AlperenAkkuncu/PlainDAQ/pics/plaindaq-band-pass.png

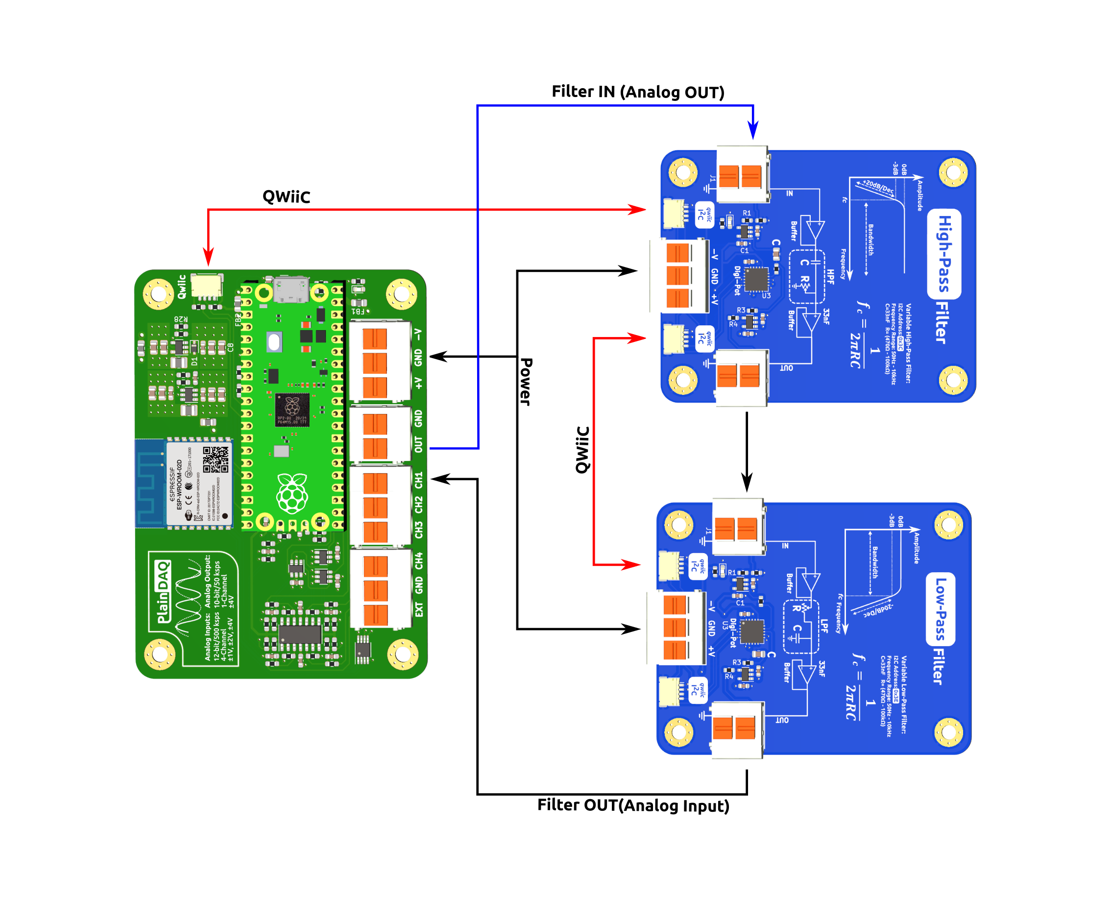
pics/plaindaq-band-pass.png
