AlperenAkkuncu/PlainDAQ/pics/plaindaq-high-pass.png

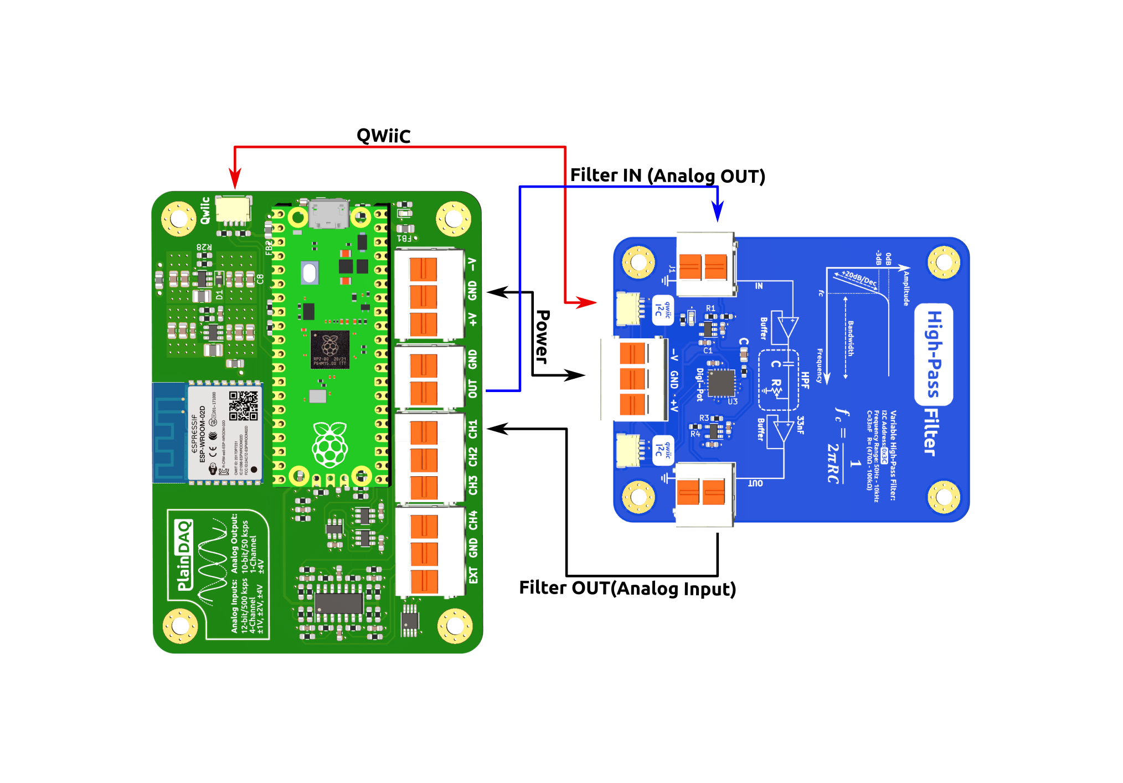
pics/plaindaq-high-pass.png
