AlperenAkkuncu/PlainDAQ/Development/SPICE_simulation/DAC_reconstruction/DAC_reconstruction.asc

C1: cap; 4.3n
C2: cap; 1.1n
C3: cap; 4.3n
C4: cap; 1.1n
C5: cap; 4.3n
C6: cap; 1.1n
R1: res; 2.05k
R2: res; 1.02k
R3: res; 2.05k
R4: res; 2.05k
R5: res; 2.05k
R6: res; 2.05k
R7: res; 2.05k
R8: res; 2.05k
R9: res; 2.05k
R10: res; 2.05k
R11: res; 2.05k
R12: res; 1.02k
R13: res; 2.05k
R14: res; 2.05k
R15: res; 2.05k
R16: res; 2.05k
R17: res; 2.05k
R18: res; 2.05k
R19: res; 2.05k
R20: res; 2.05k
R21: res; 2.05k
R22: res; 2.05k
R23: res; 1.02k
R24: res; 2.05k
R25: res; 2.05k
R26: res; 2.05k
R27: res; 2.05k
R28: res; 2.05k
R29: res; 2.05k
R30: res; 2.05k
R31: res; 2.05k
R32: res; 2.05k
R33: res; 2.05k
R34: res; 2.05k
R35: res; 2.05k
R36: res; 2.05k
R37: res; 2.05k
R38: res; 2.05k
U1: opamp2; TL072
U2: opamp2; TL072
U3: opamp2; TL072
U4: opamp2; TL072
U5: opamp2; TL072
U6: opamp2; TL072
U7: opamp2; TL072
U8: opamp2; TL072
U9: opamp2; TL072
U10: opamp2; TL072
U11: opamp2; TL072
V1: voltage; 6.5
V2: voltage; 6.5
V3: voltage; SINE(1 1 1k); AC 1
V4: voltage; 4
V5: voltage; SINE(1 1 1k); AC 1
V6: voltage; 4
V7: voltage; 1; AC 0
V8: voltage; SINE(1 1 1k); AC 1
V9: voltage; 0.8; AC 0
V10: voltage; 1; AC 0
V11: voltage; 4.096; AC 0
V12: voltage; 4.096; AC 0
Named nets: 0, +V, -V
* TL072 OPERATIONAL AMPLIFIER "MACROMODEL" SUBCIRCUIT
* CREATED USING PARTS RELEASE 4.01 ON 06/16/89 AT 13:08
* (REV N/A)      SUPPLY VOLTAGE: +/-15V
* CONNECTIONS:   NON-INVERTING INPUT
*                | INVERTING INPUT
*                | | POSITIVE POWER SUPPLY
*                | | | NEGATIVE POWER SUPPLY
*                | | | | OUTPUT
*                | | | | |
.SUBCKT TL072    1 2 3 4 5
*
  C1   11 12 3.498E-12
  C2    6  7 15.00E-12
  DC    5 53 DX
  DE   54  5 DX
  DLP  90 91 DX
  DLN  92 90 DX
  DP    4  3 DX
  EGND 99  0 POLY(2) (3,0) (4,0) 0 .5 .5
  FB    7 99 POLY(5) VB VC VE VLP VLN 0 4.715E6 -5E6 5E6 5E6 -5E6
  GA    6  0 11 12 282.8E-6
  GCM   0  6 10 99 8.942E-9
  ISS   3 10 DC 195.0E-6
  HLIM 90  0 VLIM 1K
  J1   11  2 10 JX
  J2   12  1 10 JX
  R2    6  9 100.0E3
  RD1   4 11 3.536E3
  RD2   4 12 3.536E3
  RO1   8  5 150
  RO2   7 99 150
  RP    3  4 2.143E3
  RSS  10 99 1.026E6
  VB    9  0 DC 0
  VC    3 53 DC 2.200
  VE   54  4 DC 2.200
  VLIM  7  8 DC 0
  VLP  91  0 DC 25
  VLN   0 92 DC 25
.MODEL DX D(IS=800.0E-18)
.MODEL JX PJF(IS=15.00E-12 BETA=270.1E-6 VTO=-1)
.ENDS
Multiple Feedback
.tran 10m
Multiple Feedback
Multiple Feedback
