AlperenAkkuncu/PlainDAQ/Development/SPICE_simulation/Analog_inputs/Analog_inputs.asc

R1: res; 1Meg
R2: res; 100
R3: res; 2k
R4: res; 2k
R5: res; 2k
R6: res; 2k
R7: res; 1Meg
R8: res; 100
R9: res; 2k
R10: res; 2k
R11: res; 2k
R12: res; 2k
R13: res; 2k
R14: res; 2k
R15: res; 1Meg
R16: res; 100
R17: res; 2k
R18: res; 2k
R19: res; 2k
R20: res; 2k
R21: res; 2k
R22: res; 2k
R23: res; 2k
R24: res; 2k
U1: opamp2; TL072
U2: AD8541
U3: AD8541
U4: AD8541
U5: AD8541
U6: opamp2; TL072
U7: AD8541
U8: AD8541
U9: AD8541
U10: AD8541
U11: opamp2; TL072
U12: AD8541
U13: AD8541
U14: AD8541
U15: AD8541
V1: voltage; 6.5
V2: voltage; 6.5
V3: voltage; SINE(0 4 1k); AC 1
V4: voltage; 4
V5: voltage; 5
V6: voltage; 2
V7: voltage; SINE(0 1 1k); AC 1
V8: voltage; SINE(0 2 1k); AC 1
Named nets: 0, +V, -V, bias, +5V, bias/2
.tran 10m
* TL072 OPERATIONAL AMPLIFIER "MACROMODEL" SUBCIRCUIT
* CREATED USING PARTS RELEASE 4.01 ON 06/16/89 AT 13:08
* (REV N/A)      SUPPLY VOLTAGE: +/-15V
* CONNECTIONS:   NON-INVERTING INPUT
*                | INVERTING INPUT
*                | | POSITIVE POWER SUPPLY
*                | | | NEGATIVE POWER SUPPLY
*                | | | | OUTPUT
*                | | | | |
.SUBCKT TL072    1 2 3 4 5
*
  C1   11 12 3.498E-12
  C2    6  7 15.00E-12
  DC    5 53 DX
  DE   54  5 DX
  DLP  90 91 DX
  DLN  92 90 DX
  DP    4  3 DX
  EGND 99  0 POLY(2) (3,0) (4,0) 0 .5 .5
  FB    7 99 POLY(5) VB VC VE VLP VLN 0 4.715E6 -5E6 5E6 5E6 -5E6
  GA    6  0 11 12 282.8E-6
  GCM   0  6 10 99 8.942E-9
  ISS   3 10 DC 195.0E-6
  HLIM 90  0 VLIM 1K
  J1   11  2 10 JX
  J2   12  1 10 JX
  R2    6  9 100.0E3
  RD1   4 11 3.536E3
  RD2   4 12 3.536E3
  RO1   8  5 150
  RO2   7 99 150
  RP    3  4 2.143E3
  RSS  10 99 1.026E6
  VB    9  0 DC 0
  VC    3 53 DC 2.200
  VE   54  4 DC 2.200
  VLIM  7  8 DC 0
  VLP  91  0 DC 25
  VLN   0 92 DC 25
.MODEL DX D(IS=800.0E-18)
.MODEL JX PJF(IS=15.00E-12 BETA=270.1E-6 VTO=-1)
.ENDS
1X RANGE
2X RANGE
4X RANGE
